xzh1179/oled_keyboard/doc/671.webp

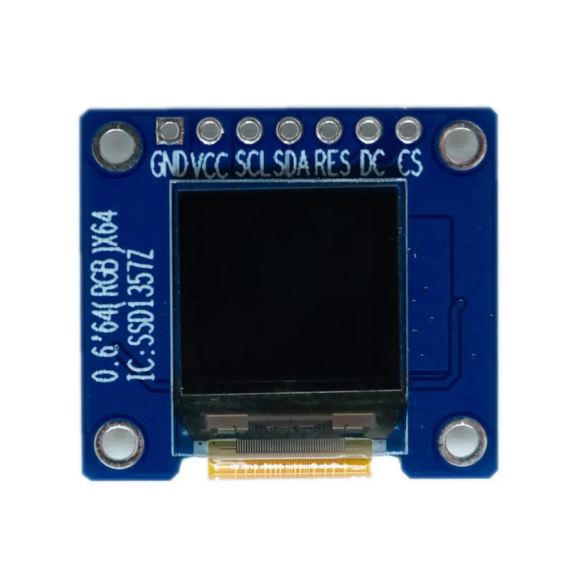
doc/671.webp
