xzh1179/oled_keyboard/doc/671_3.webp

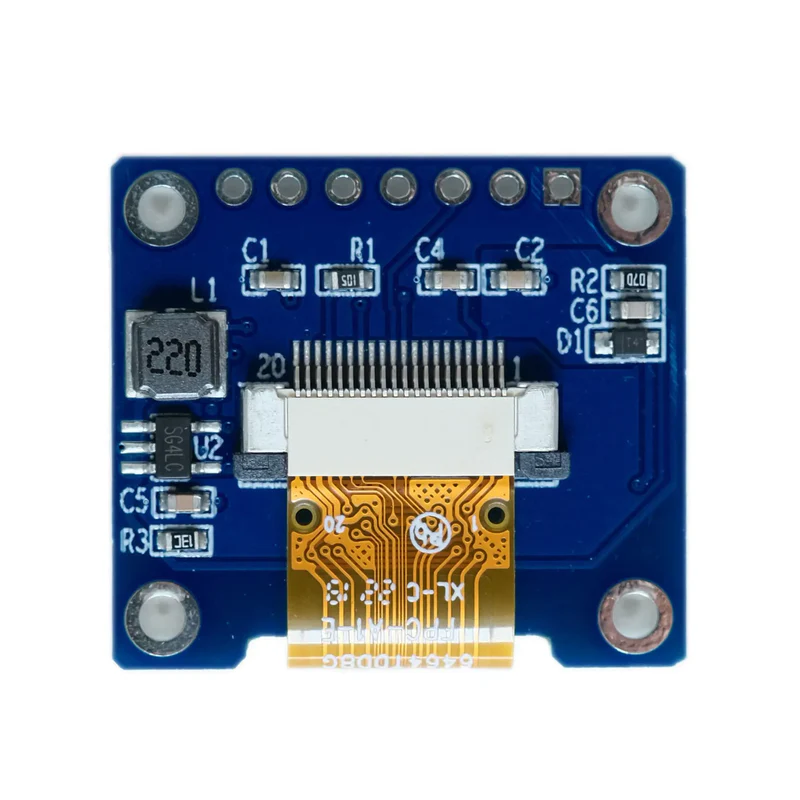
doc/671_3.webp
