xzh1179/oled_keyboard/samples/piantor/piantor-main/case/side.jpg

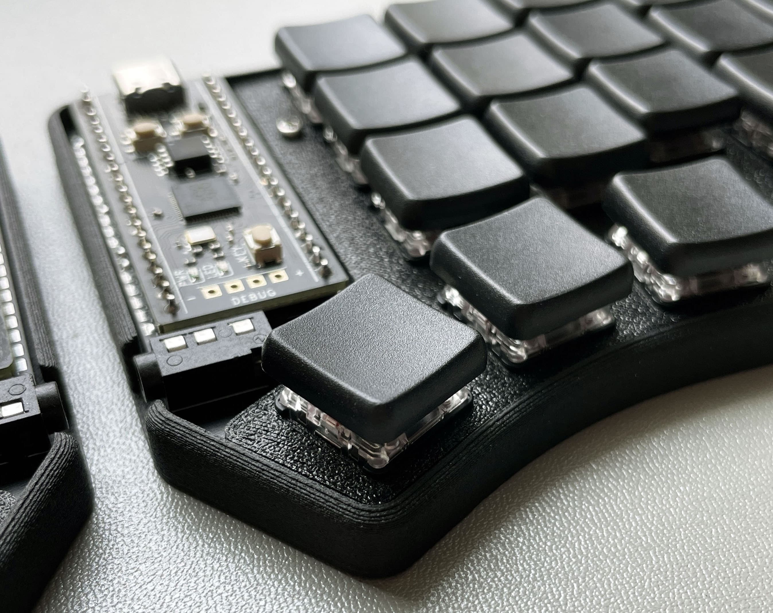
samples/piantor/piantor-main/case/side.jpg
