xzh1179/oled_keyboard/samples/piantor/piantor-main/case/top.jpg

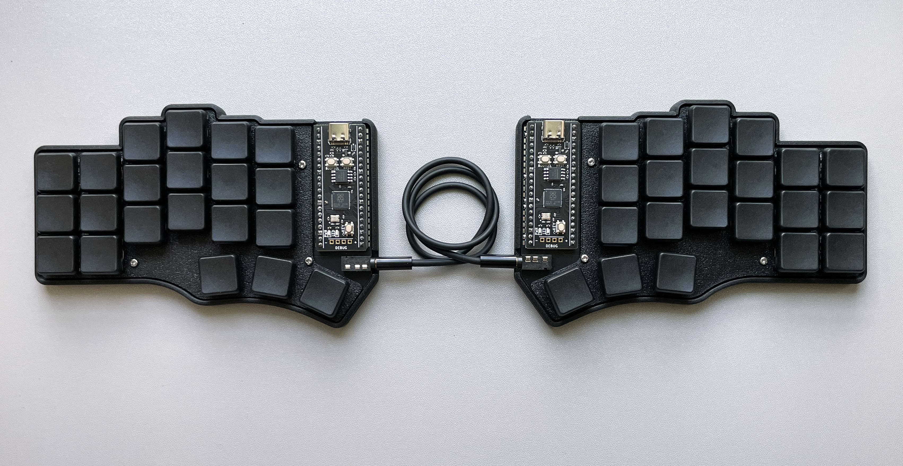
samples/piantor/piantor-main/case/top.jpg
