xzh1179/oled_keyboard/samples/piantor/piantor-main/docs/beekeeb.png

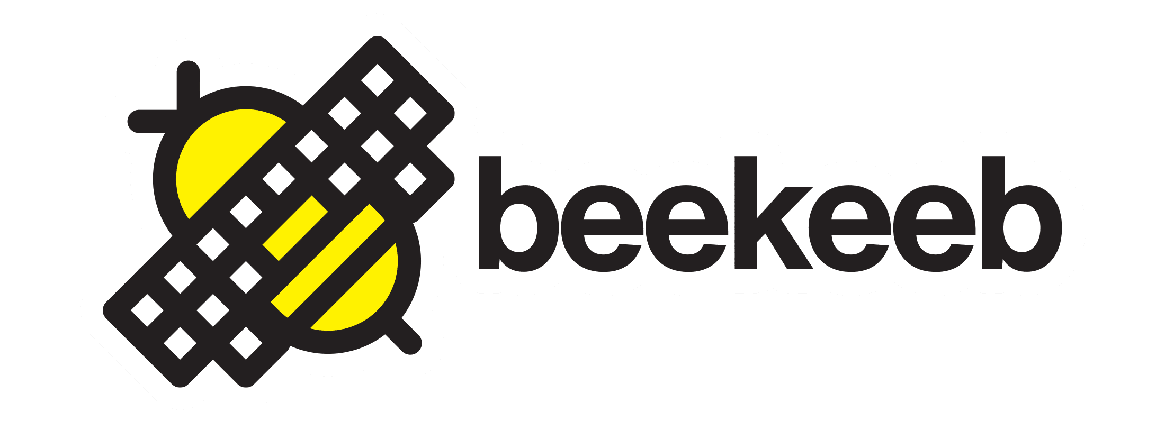
samples/piantor/piantor-main/docs/beekeeb.png
