xzh1179/oled_keyboard/samples/piantor/piantor-main/docs/keyboard_right.png

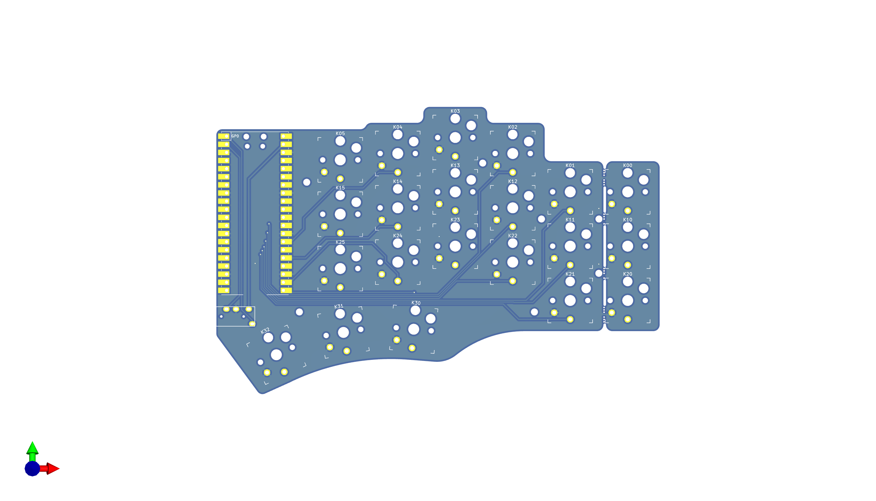
samples/piantor/piantor-main/docs/keyboard_right.png
