xzh1179/oled_keyboard/samples/piantor/piantor-main/docs/left-back.png

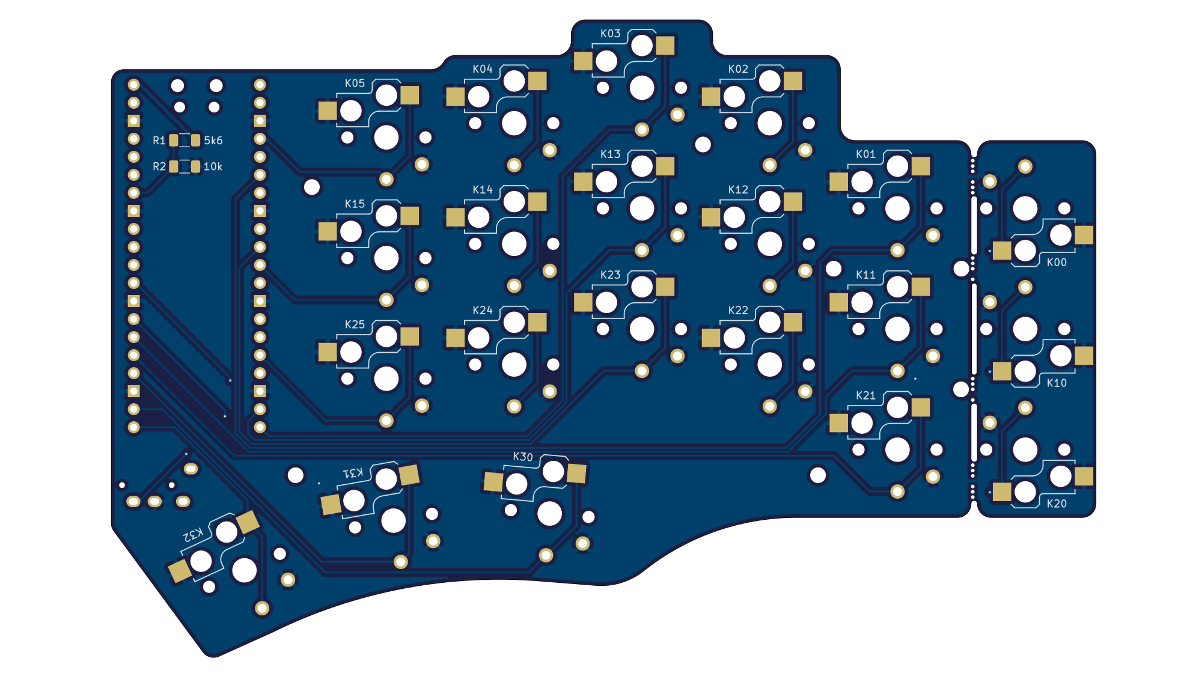
samples/piantor/piantor-main/docs/left-back.png
