xzh1179/oled_keyboard/samples/piantor/piantor-main/docs/left-front.png

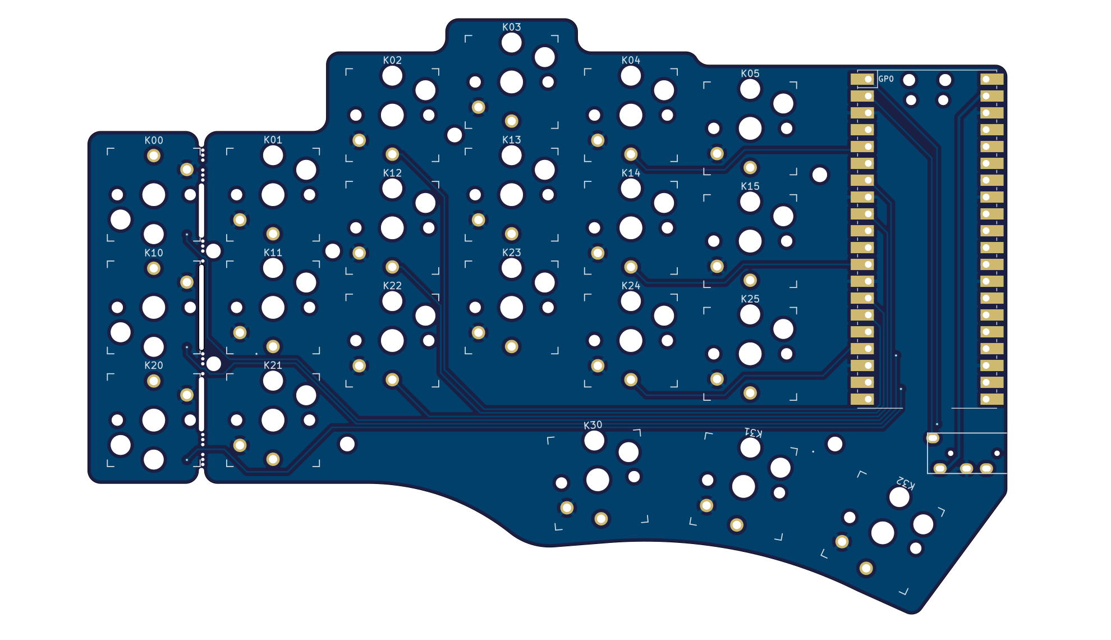
samples/piantor/piantor-main/docs/left-front.png
