xzh1179/oled_keyboard/samples/piantor/piantor-main/docs/pcbway.png

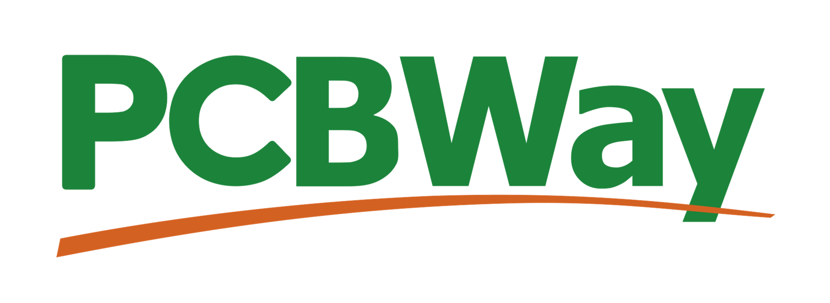
samples/piantor/piantor-main/docs/pcbway.png
