xzh1179/oled_keyboard/samples/piantor/piantor-main/docs/right-back.png

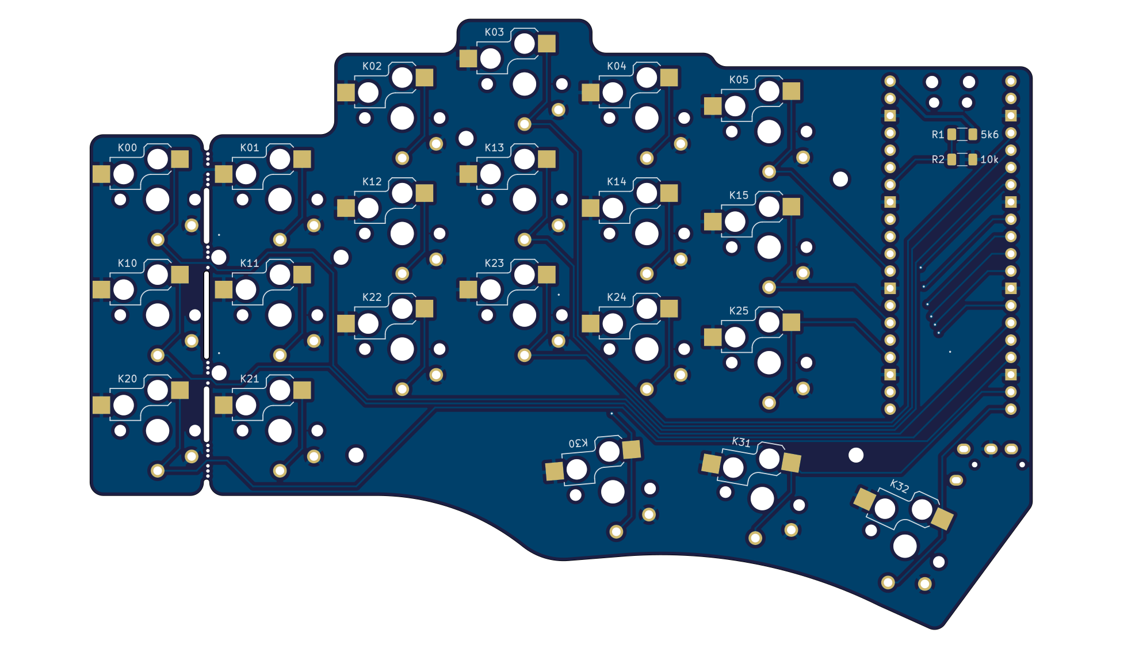
samples/piantor/piantor-main/docs/right-back.png
