xzh1179/oled_keyboard/samples/piantor/piantor-main/docs/right-front.png

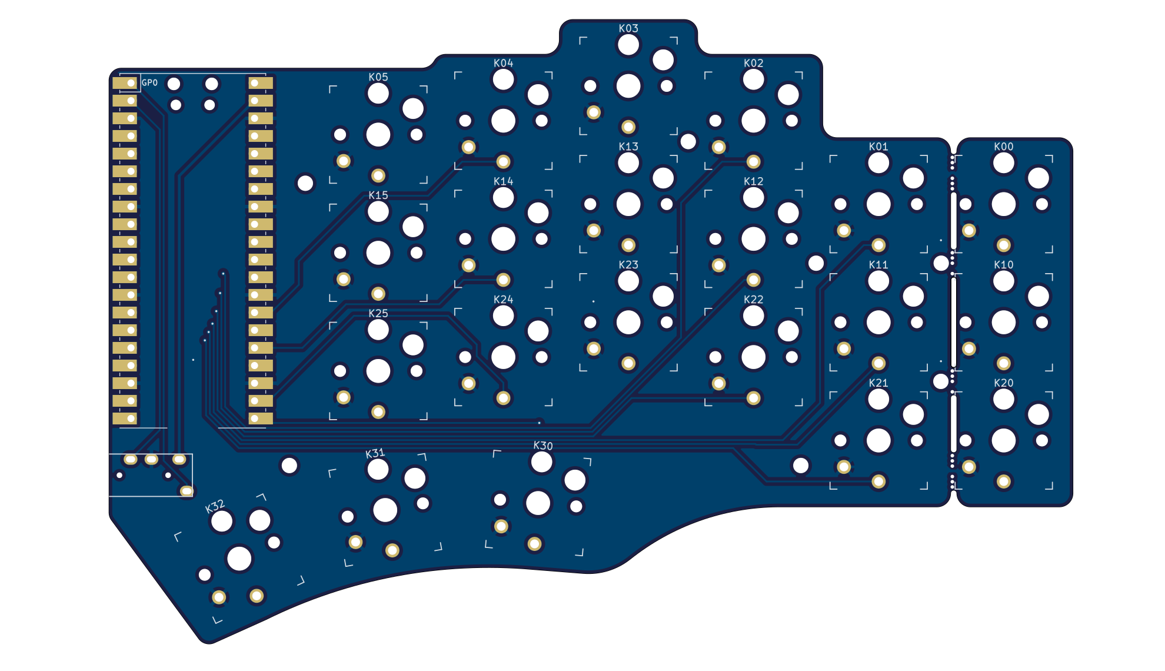
samples/piantor/piantor-main/docs/right-front.png
