xzh1179/oled_keyboard/kiswitch-main/kiswitch-main/source_3d/Switch_Keyboard_Kailh/SW_Hotswap_Kailh_Choc_v1.FCStd

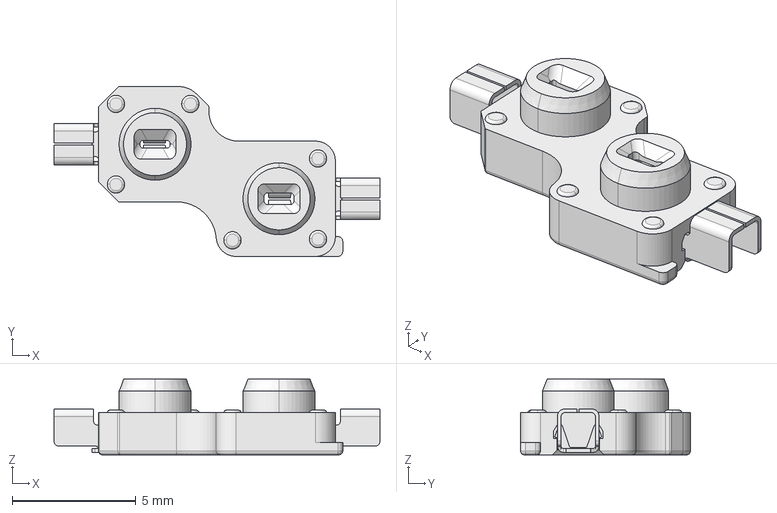
[picture p31: CAD file, 2026-02-28]
kiswitch-main/kiswitch-main/source_3d/Switch_Keyboard_Kailh/SW_Hotswap_Kailh_Choc_v1.FCStd
13.2 x 6.85 x 3.05 mm
