xzh1179/oled_keyboard/shell/cover.SLDPRT

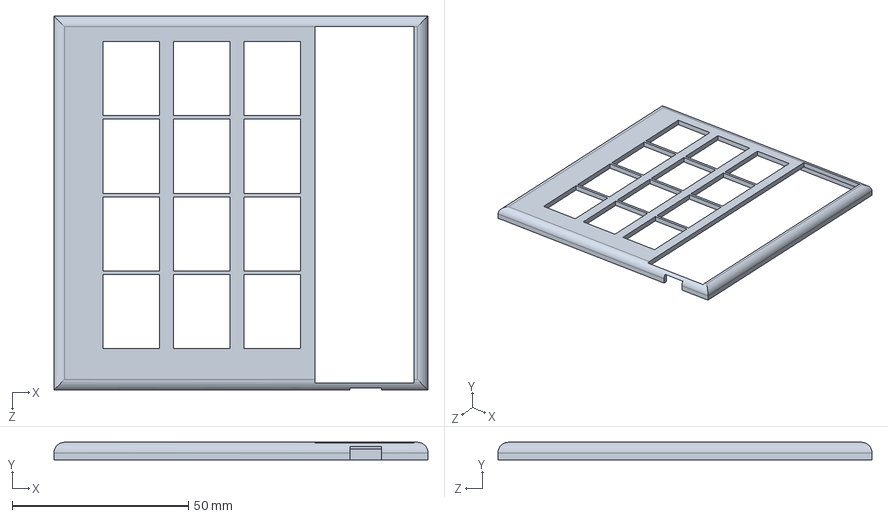
[picture p32: CAD file, 2026-09-15]
shell/cover.SLDPRT
106.0 x 5.00 x 106.0 mm
