xzh1179/oled_keyboard/shell/shell - cover-1 - bottom-1.STL

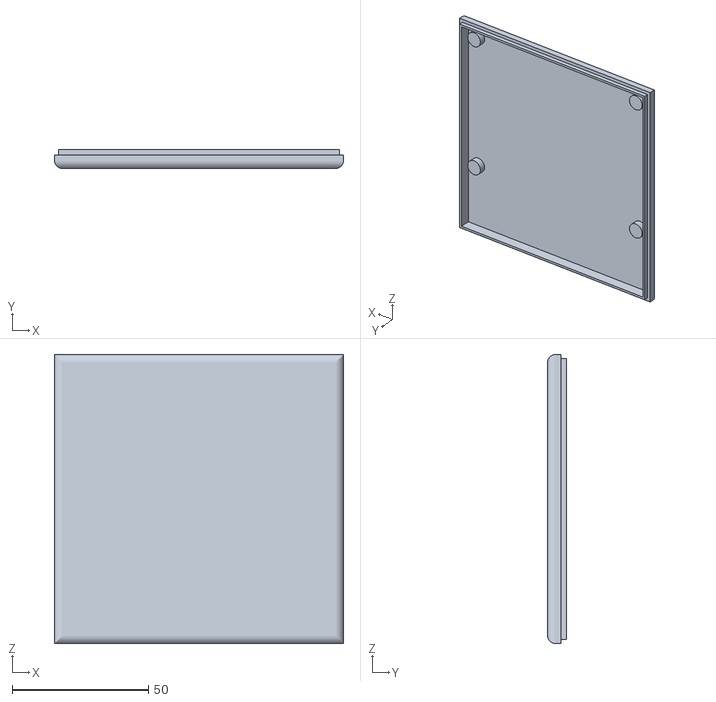
[picture p34: CAD file, 2026-09-15]
shell/shell - cover-1 - bottom-1.STL
106.0 x 7.00 x 106.0
