xzh1179/oled_keyboard/kiswitch-main/kiswitch-main/source_3d/Mounting_Keyboard_Stabilizer/Stabilizer_Cherry_MX_3u.FCStd

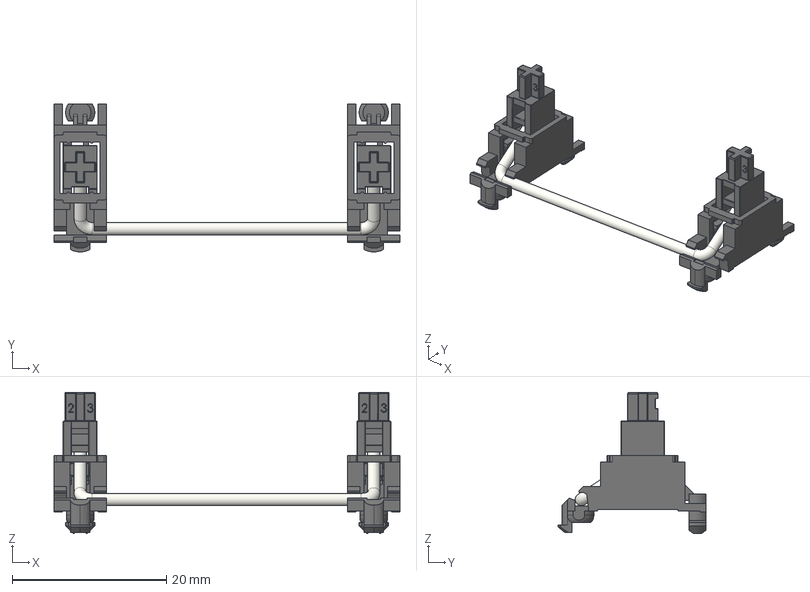
[picture p35: CAD file, 2026-02-28]
kiswitch-main/kiswitch-main/source_3d/Mounting_Keyboard_Stabilizer/Stabilizer_Cherry_MX_3u.FCStd
44.9 x 19.2 x 18.3 mm
Bar
Stabilizer_Key_
Stabilizer_Base_
Stabilizer_Key
Stabilizer_Base
