xzh1179/oled_keyboard/shell/oled_keyboard.step

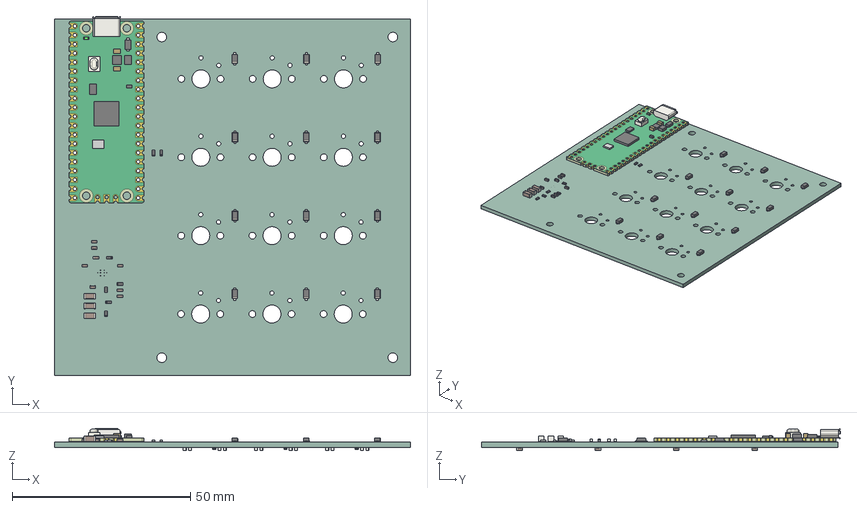
[picture p37: CAD file, 2026-09-15]
shell/oled_keyboard.step
100.0 x 100.8 x 6.18 mm
D_SOD-123F x 12
C_0603_1608Metric x 56
R_0603_1608Metric x 19
RaspberryPi_Pico_Module_KiCad
C_1206_3216Metric x 3
oled_keyboard_PCB
