xzh1179/oled_keyboard/shell/display_support.SLDPRT

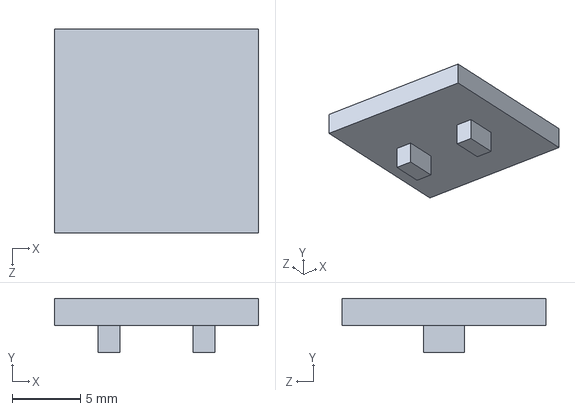
[picture p38: CAD file, 2026-09-15]
shell/display_support.SLDPRT
15.0 x 4.00 x 15.0 mm
