xzh1179/oled_keyboard/shell/Assem1.SLDASM

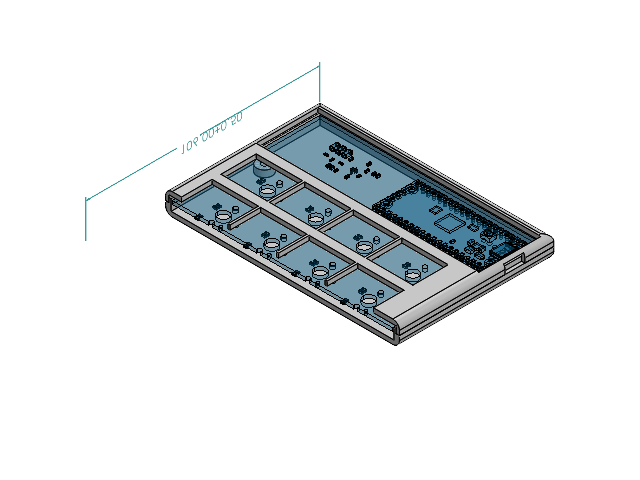
[picture p39: CAD file, 2026-09-15]
shell/Assem1.SLDASM
bottom
RaspberryPi_Pico_Module_KiCad.step
D_SOD-123F.step x 12
C_0603_1608Metric.step x 56
R_0603_1608Metric.step x 19
C_1206_3216Metric.step x 3
oled_keyboard_PCB.step
cover
